UniversalScientificTechnologies/IRRADROOM01/irradroom_python/irradroom_python/door_status.py

import rclpy
import serial
import time
from rclpy.node import Node

from std_msgs.msg import Int8
import odroid_wiringpi as wpi

class DoorStatus(Node):

    def __init__(self):
        super().__init__("door_status")
        self.publisher = self.create_publisher(Int8, "door_status", 10)
        timer = 0.5
        self.status = -1

        wpi.wiringPiSetup()
        wpi.pinMode(27, 0)
        wpi.pullUpDnControl(27, 2)

        wpi.pinMode(4, 1)
        wpi.pinMode(3, 1)
        self.timer = self.create_timer(timer, self.measure)
        self.i = 0


    def measure(self):
        try:
            msg = Int8()
            msg.data = wpi.digitalRead(27)
            print("status:", msg.data)
            self.publisher.publish(msg)
            if msg.data != self.status:
                print("Zmena", msg.data)
                if msg.data:
                    print("ON")
                    wpi.digitalWrite(3, 0)
                    wpi.digitalWrite(4, 1)
                else:
                    print("OFF")
                    wpi.digitalWrite(3, 0)
                    wpi.digitalWrite(4, 1)
            self.status = msg.data
        except Exception as e:
            print(e)

def main(args=None):
    rclpy.init(args=args)
    sp = DoorStatus()
    rclpy.spin(sp)

    sp.destroy_node()
    rclpy.shutdown()

if __name__ == '__main__':
    main()
